billyen33/Portable_UV_Index_Meter/Burn_Meter/bitmap.h

#ifndef BITMAP_H
#define BITMAP_H

//Face is 60W*69H pixels, in R5G6B5 format

const uint16_t face[] PROGMEM = {
0x0000, 0x0000, 0x0000, 0x0000, 0x0000, 0x0000, 0x0000, 0x0000, 0x0000, 0x0000, 0x0020, 0x0000, 0x0000, 0x0000, 0x0000, 0x0000, 0x0000, 0x0000, 0x0000, 0x0020, 0x0000, 0x0000, 0x0000, 0x0800, 0x0000, 0x0000, 0x0800, 0x2903, 0x2904, 0x0820, 0x0000, 0x0000, 0x0000, 0x0000, 0x0000, 0x0000, 0x0000, 0x0000, 0x0000, 0x0000, 0x0000, 0x0000, 0x0001, 0x0000, 0x0000, 0x0000, 0x0000, 0x0000, 0x0000, 0x0000, 0x0000, 0x0000, 0x0000, 0x0000, 0x0000, 0x0000, 0x0000, 0x0000, 0x0000, 0x0000, 
0x0000, 0x0000, 0x0000, 0x0000, 0x0000, 0x0000, 0x0000, 0x0000, 0x0020, 0x0000, 0x0000, 0x0841, 0x0000, 0x0000, 0x0000, 0x0000, 0x0000, 0x0800, 0x0000, 0x20c2, 0x5a69, 0x6aeb, 0x62ca, 0x6b0b, 0x732b, 0x734c, 0x838d, 0x944f, 0x83ee, 0x62c9, 0x5a88, 0x5aa9, 0x736c, 0x5a89, 0x2944, 0x0820, 0x0000, 0x0000, 0x0000, 0x0000, 0x0000, 0x0000, 0x0000, 0x0000, 0x0000, 0x0020, 0x0000, 0x0000, 0x0000, 0x0000, 0x0000, 0x0000, 0x0000, 0x0000, 0x0000, 0x0000, 0x0000, 0x0000, 0x0000, 0x0000, 
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
0x946c, 0xc58d, 0xee48, 0xf5c2, 0xfd40, 0xfd40, 0xfce0, 0xf440, 0xf3e3, 0xf345, 0xfa88, 0xf9e9, 0xf109, 0xf089, 0xe84a, 0xf009, 0xf808, 0xf807, 0xf007, 0xd8a7, 0xf430, 0xed32, 0xbbce, 0xdcb2, 0xe4d2, 0xdc91, 0xd451, 0xdc92, 0xdcb1, 0xd490, 0xd491, 0xd42f, 0xf492, 0xebaf, 0xdaca, 0xd246, 0xda23, 0xea62, 0xf2c2, 0xfb21, 0xfbc1, 0xf440, 0xf4c1, 0xed23, 0xed48, 0xe54c, 0xdd0f, 0xd4f1, 0xd4f1, 0xd512, 0xc4b1, 0xccf2, 0xbc70, 0xccd2, 0xccf2, 0x92ea, 0x9aeb, 0xc451, 0xc431, 0x92ec, 
0x2940, 0x49e0, 0x9be1, 0xfe66, 0xfdc2, 0xfd20, 0xfd40, 0xfca0, 0xfc22, 0xf384, 0xfae6, 0xfa68, 0xf9a9, 0xf129, 0xe8a9, 0xe848, 0xf026, 0xe806, 0xe026, 0xe18a, 0xfcf3, 0xb3ee, 0xc430, 0xdcb2, 0xe4b2, 0xdc70, 0xdc92, 0xd451, 0xd491, 0xd4b1, 0xc40f, 0xc40f, 0xcc10, 0xdc50, 0xec4f, 0xebcc, 0xe327, 0xe2e4, 0xeb03, 0xeb63, 0xf3e2, 0xec63, 0xecc5, 0xe528, 0xe52c, 0xe52f, 0xdd31, 0xdd12, 0xd512, 0xccd1, 0xccf2, 0xc491, 0xc4b1, 0xd512, 0xc470, 0xab6c, 0x92ca, 0xbc0f, 0xccb3, 0x8aec, 
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
}
*/
#endif
